TheForgotensoul/3D-printed_Myo-electric-prosthetic-hand/Printable Files/Fingers/Pinky/Pinky Finger Middle.STL

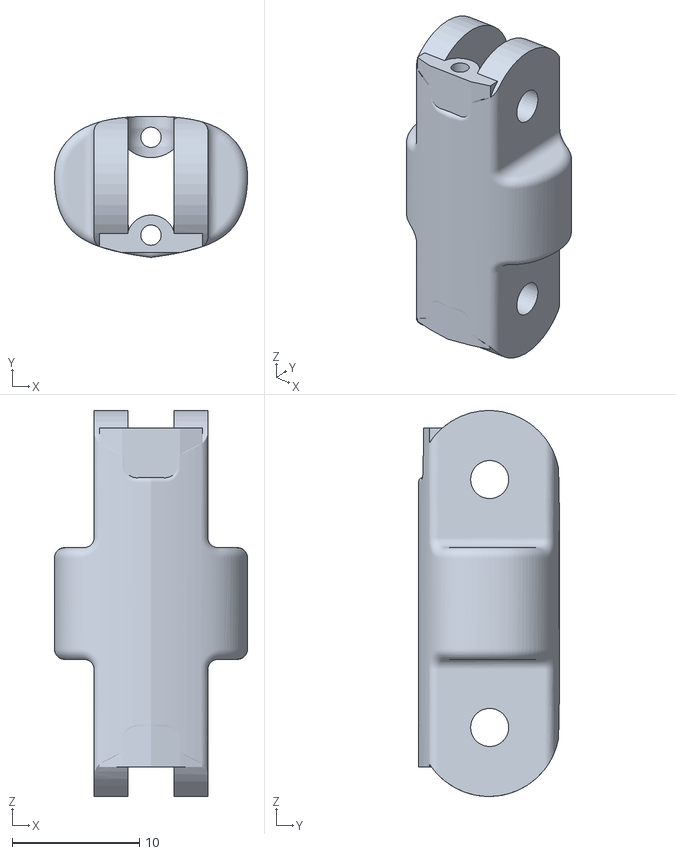
[picture p68: CAD file, 2020-09-28]
Printable Files/Fingers/Pinky/Pinky Finger Middle.STL
15.2 x 11.1 x 30.4
