TheForgotensoul/3D-printed_Myo-electric-prosthetic-hand/Printable Files/Fingers/Ring/Ring Finger Bottom Plus Cutout.STL

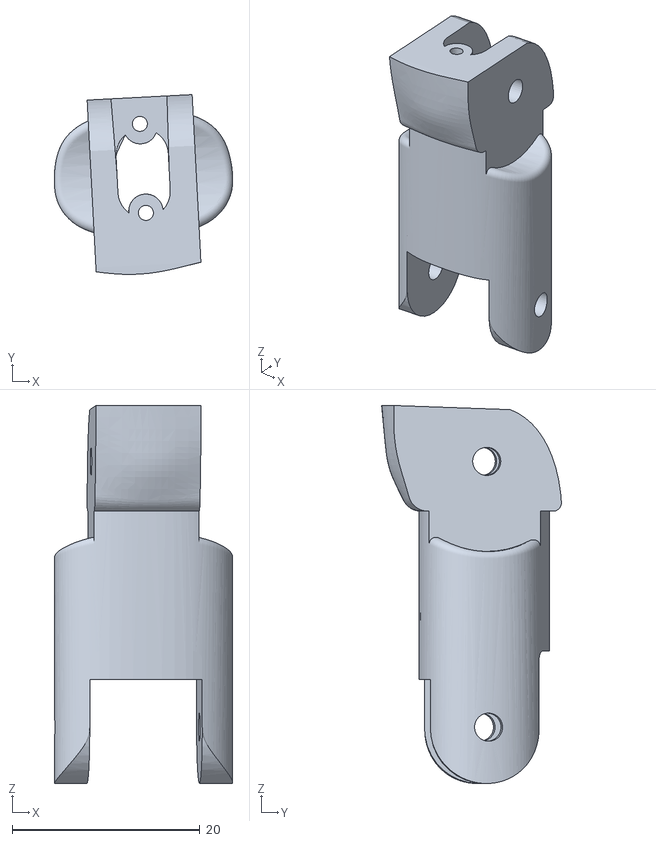
[picture p69: CAD file, 2020-09-28]
Printable Files/Fingers/Ring/Ring Finger Bottom Plus Cutout.STL
19.0 x 19.2 x 40.3
