TheForgotensoul/3D-printed_Myo-electric-prosthetic-hand/Printable Files/Fingers/Thumb/Thumb Lower.STL

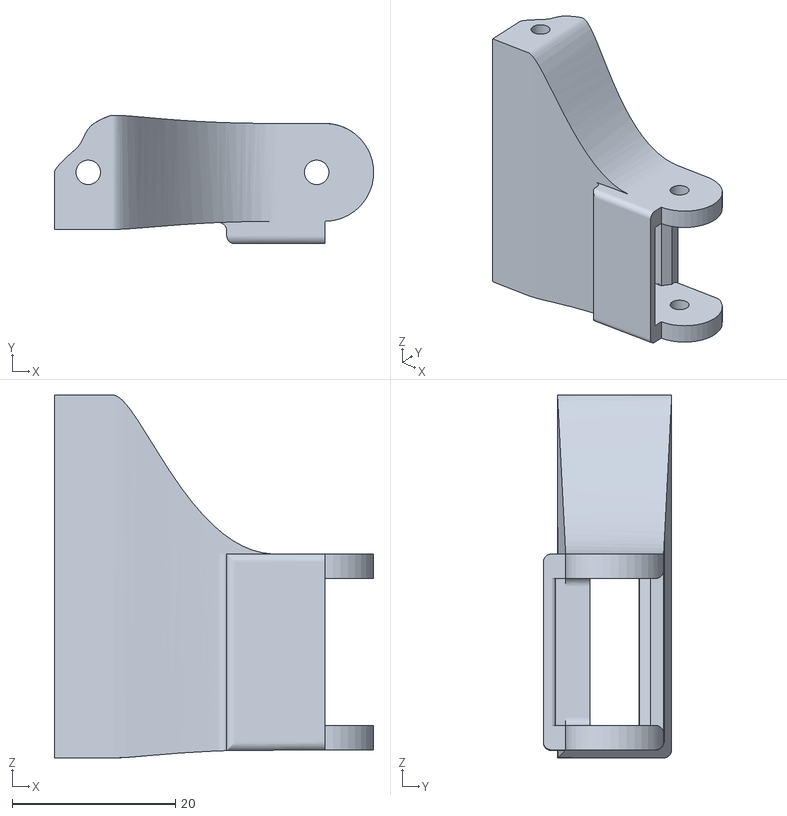
[picture p70: CAD file, 2020-09-28]
Printable Files/Fingers/Thumb/Thumb Lower.STL
39.1 x 15.8 x 44.5
