TheForgotensoul/3D-printed_Myo-electric-prosthetic-hand/Printable Files/Forearm/wrist clearance A.STL

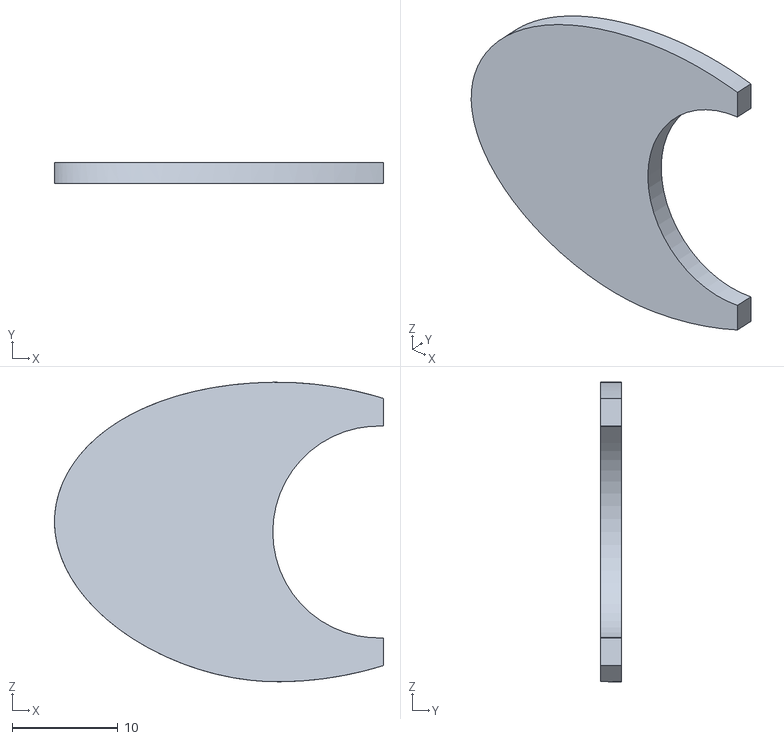
[picture p71: CAD file, 2020-09-28]
Printable Files/Forearm/wrist clearance A.STL
31.0 x 2.00 x 28.3
