TheForgotensoul/3D-printed_Myo-electric-prosthetic-hand/Printable Files/Horn.STL

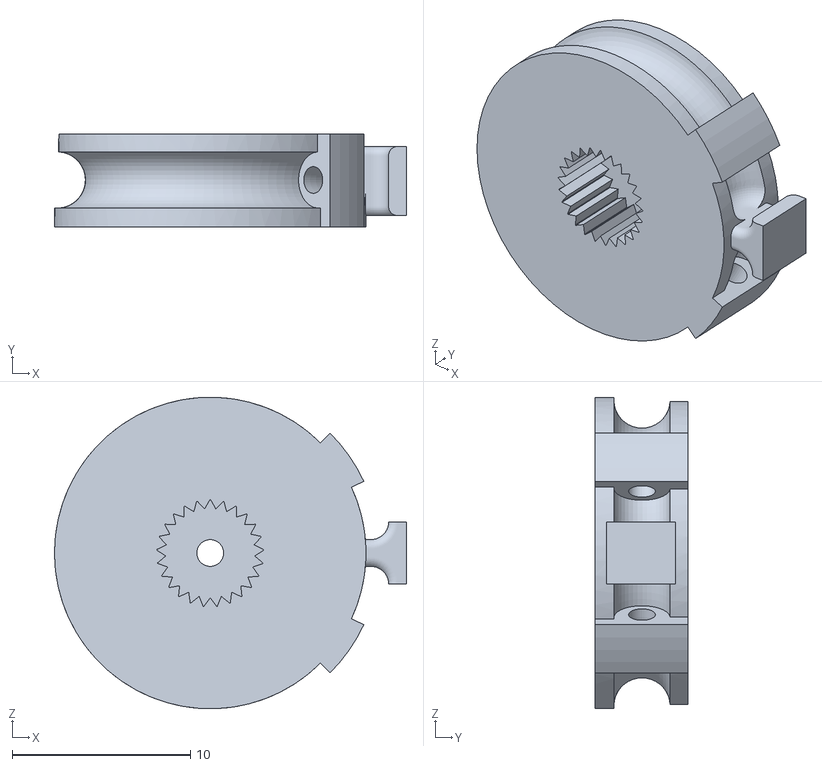
[picture p72: CAD file, 2020-09-28]
Printable Files/Horn.STL
19.7 x 5.20 x 17.5
