TheForgotensoul/3D-printed_Myo-electric-prosthetic-hand/Printable Files/Palm/Palm _ Optimised Connector.STL

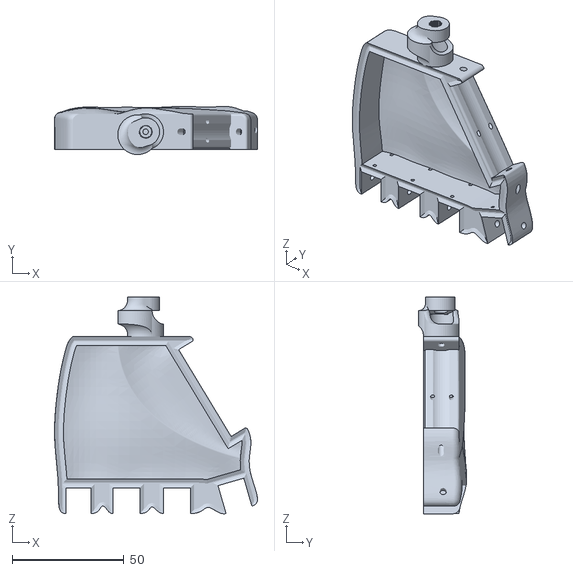
[picture p73: CAD file, 2020-09-28]
Printable Files/Palm/Palm _ Optimised Connector.STL
90.8 x 21.5 x 96.9
