TheForgotensoul/3D-printed_Myo-electric-prosthetic-hand/Printable Files/Upper Forearm/Upper Forearm Large.STL

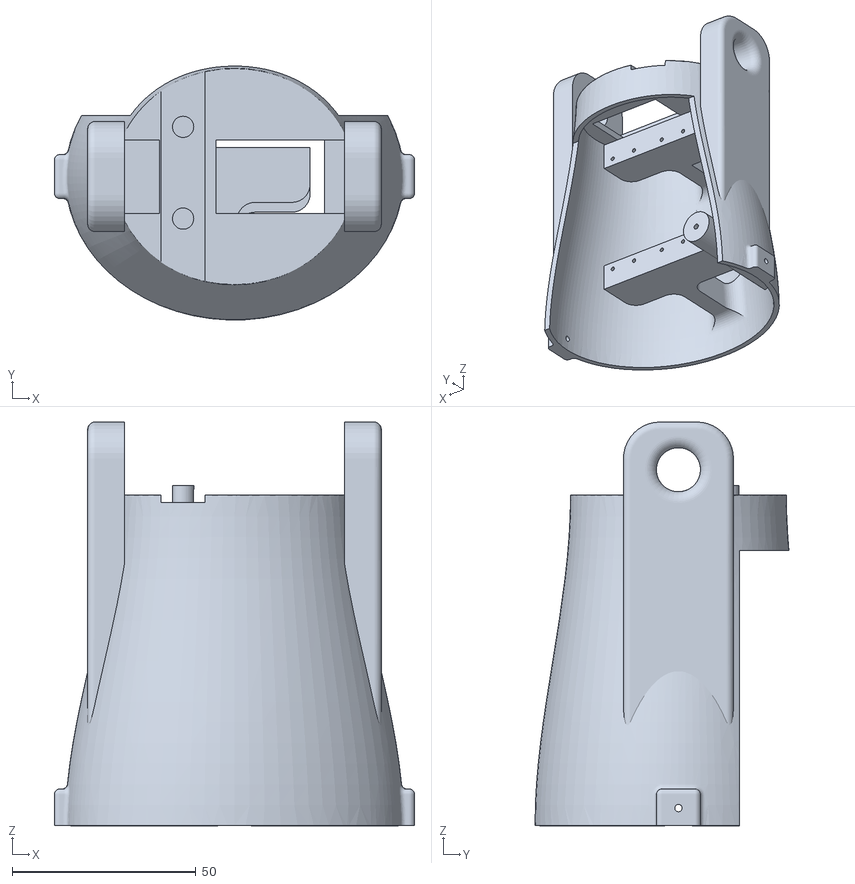
[picture p74: CAD file, 2020-09-28]
Printable Files/Upper Forearm/Upper Forearm Large.STL
98.2 x 69.2 x 110.1
