TheForgotensoul/3D-printed_Myo-electric-prosthetic-hand/Printable Files/Elbow/Small Gear.STL

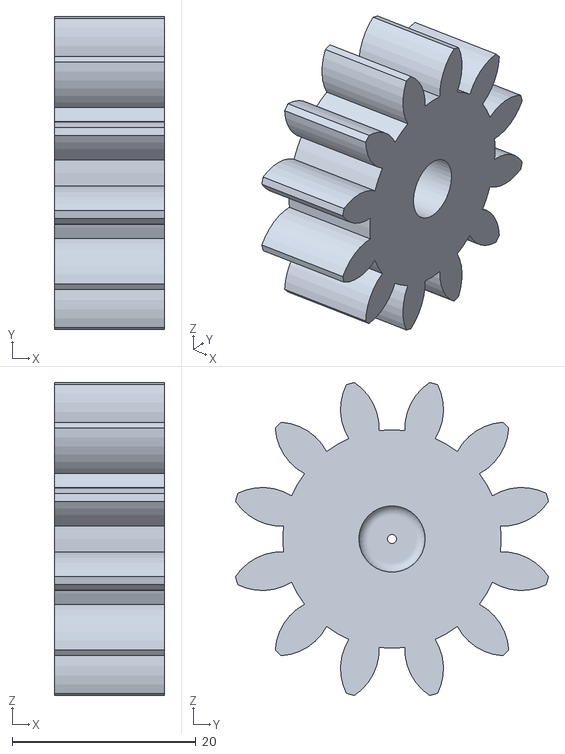
[picture p75: CAD file, 2020-09-28]
Printable Files/Elbow/Small Gear.STL
12.0 x 34.0 x 34.0
