TheForgotensoul/3D-printed_Myo-electric-prosthetic-hand/Printable Files/Fingers/Index/Index Finger Bottom Plus Cutout.STL

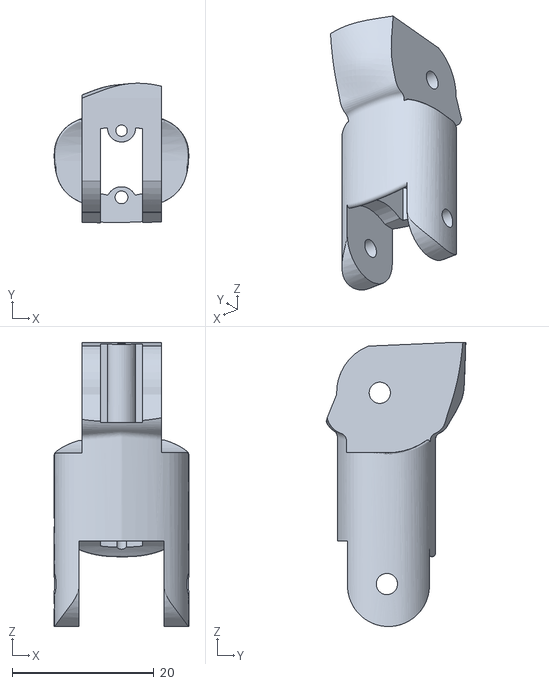
[picture p76: CAD file, 2020-09-28]
Printable Files/Fingers/Index/Index Finger Bottom Plus Cutout.STL
19.0 x 19.7 x 40.1
