TheForgotensoul/3D-printed_Myo-electric-prosthetic-hand/Printable Files/Fingers/Pinky/Pinky Finger Tip.STL

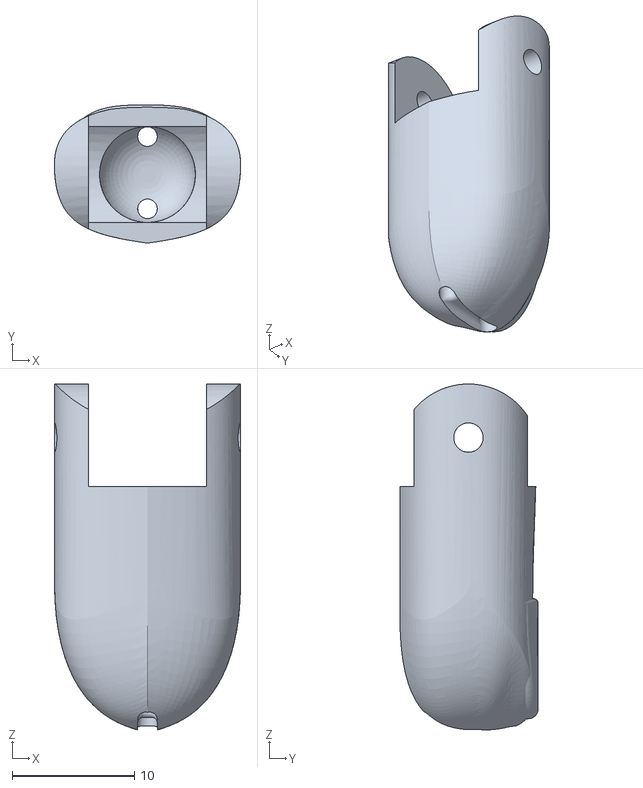
[picture p77: CAD file, 2020-09-28]
Printable Files/Fingers/Pinky/Pinky Finger Tip.STL
15.2 x 11.3 x 28.3
