TheForgotensoul/3D-printed_Myo-electric-prosthetic-hand/Printable Files/Fingers/Thumb/Thumb Middle.STL

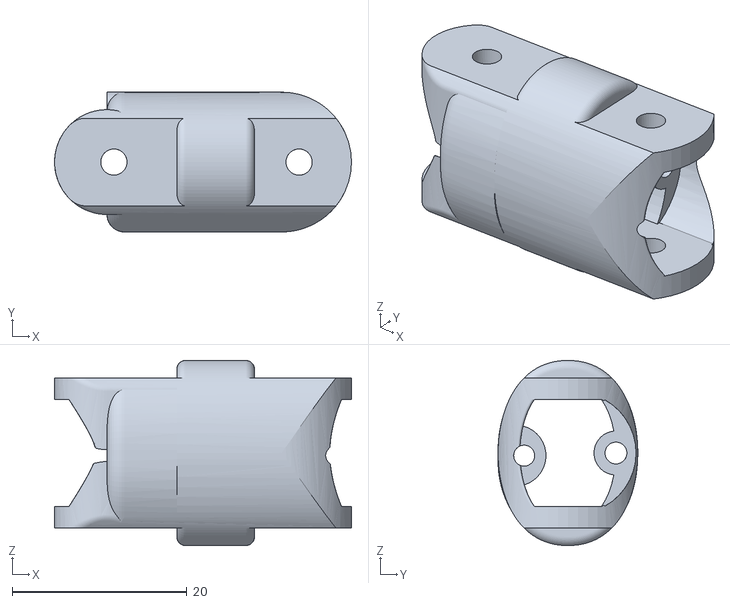
[picture p78: CAD file, 2020-09-28]
Printable Files/Fingers/Thumb/Thumb Middle.STL
34.0 x 16.0 x 21.2
