TheForgotensoul/3D-printed_Myo-electric-prosthetic-hand/Printable Files/Forearm/Mid Forearm Small.STL

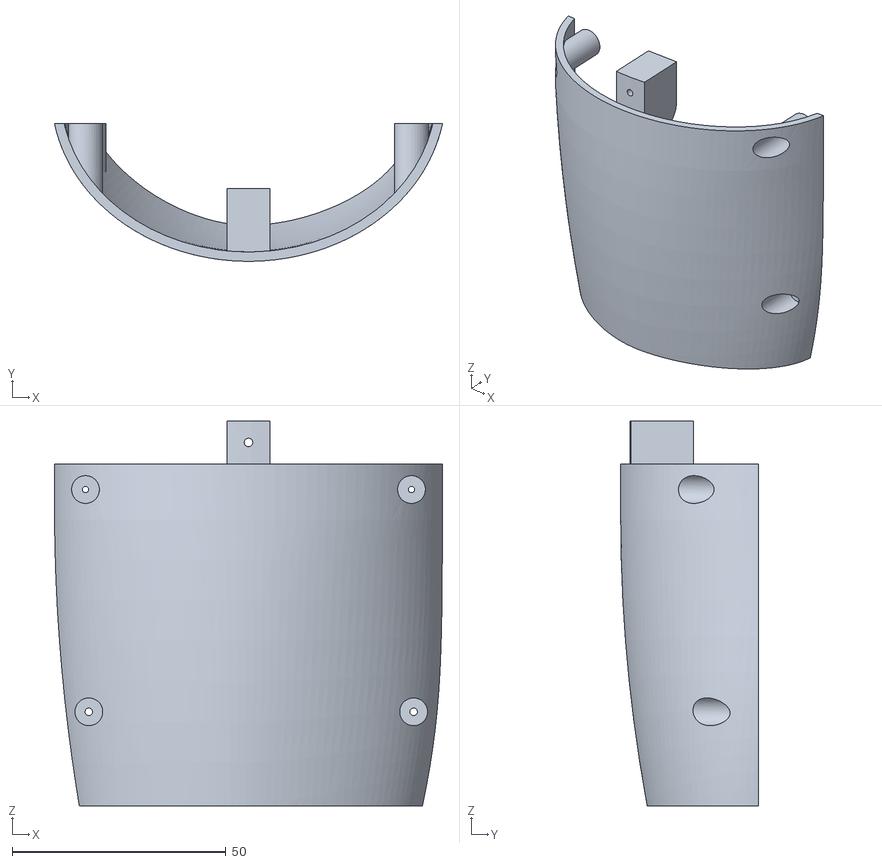
[picture p79: CAD file, 2020-09-28]
Printable Files/Forearm/Mid Forearm Small.STL
90.8 x 32.2 x 90.0
