TheForgotensoul/3D-printed_Myo-electric-prosthetic-hand/Printable Files/Upper Forearm/Forearm Gear Split.STL

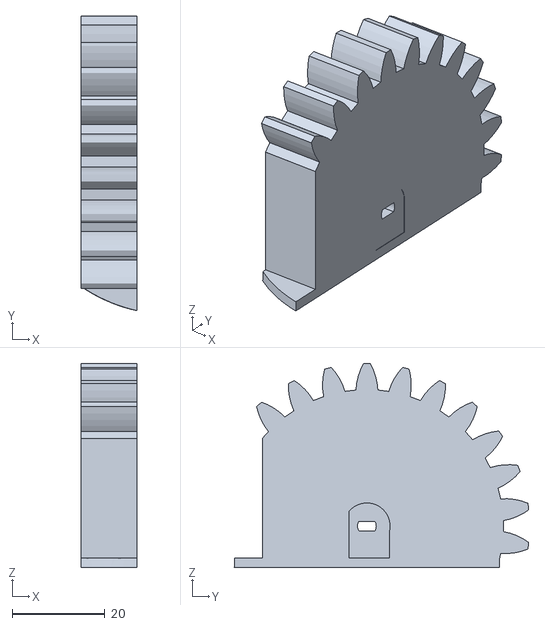
[picture p80: CAD file, 2020-09-28]
Printable Files/Upper Forearm/Forearm Gear Split.STL
12.0 x 63.4 x 43.9
