TheForgotensoul/3D-printed_Myo-electric-prosthetic-hand/Printable Files/Forearm/Wrist Forearm Section A.STL

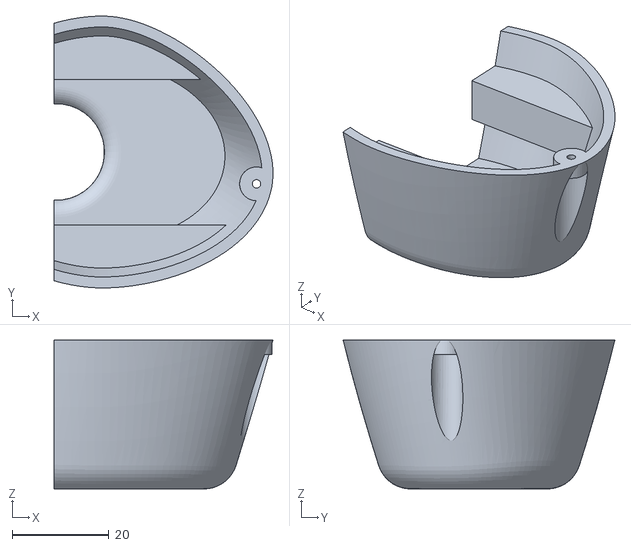
[picture p81: CAD file, 2020-09-28]
Printable Files/Forearm/Wrist Forearm Section A.STL
45.4 x 56.3 x 30.9
