TheForgotensoul/3D-printed_Myo-electric-prosthetic-hand/Printable Files/Forearm/wrist clearance B.STL

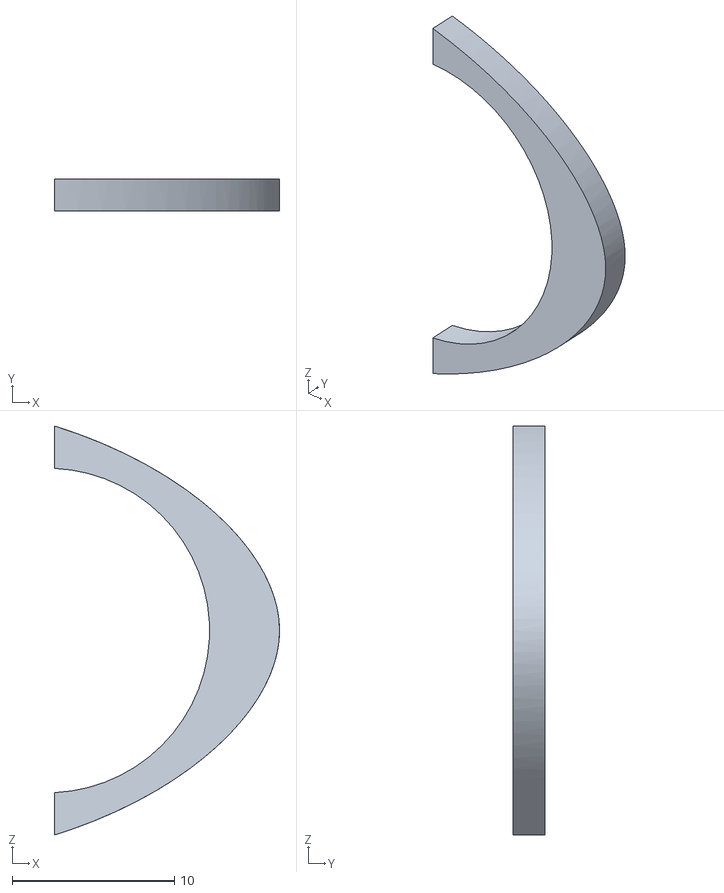
[picture p82: CAD file, 2020-09-28]
Printable Files/Forearm/wrist clearance B.STL
13.9 x 2.00 x 25.2
