TheForgotensoul/3D-printed_Myo-electric-prosthetic-hand/Printable Files/Forearm/Wrist Forearm Section B.STL

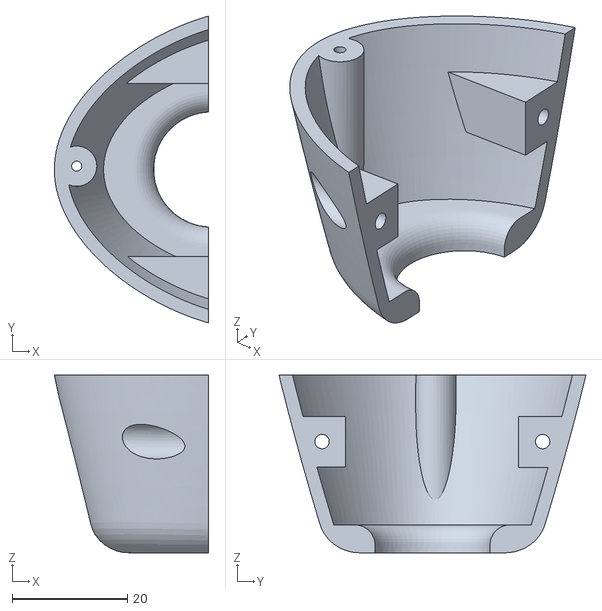
[picture p83: CAD file, 2020-09-28]
Printable Files/Forearm/Wrist Forearm Section B.STL
26.8 x 53.3 x 30.9
